Florida-Poly-IEEE-Computer-Society/Escape-Room/KiCad/Module 1/Module 1.kicad_pcb

## KiCad design Wiring/Multiplex Madness.kicad_sch

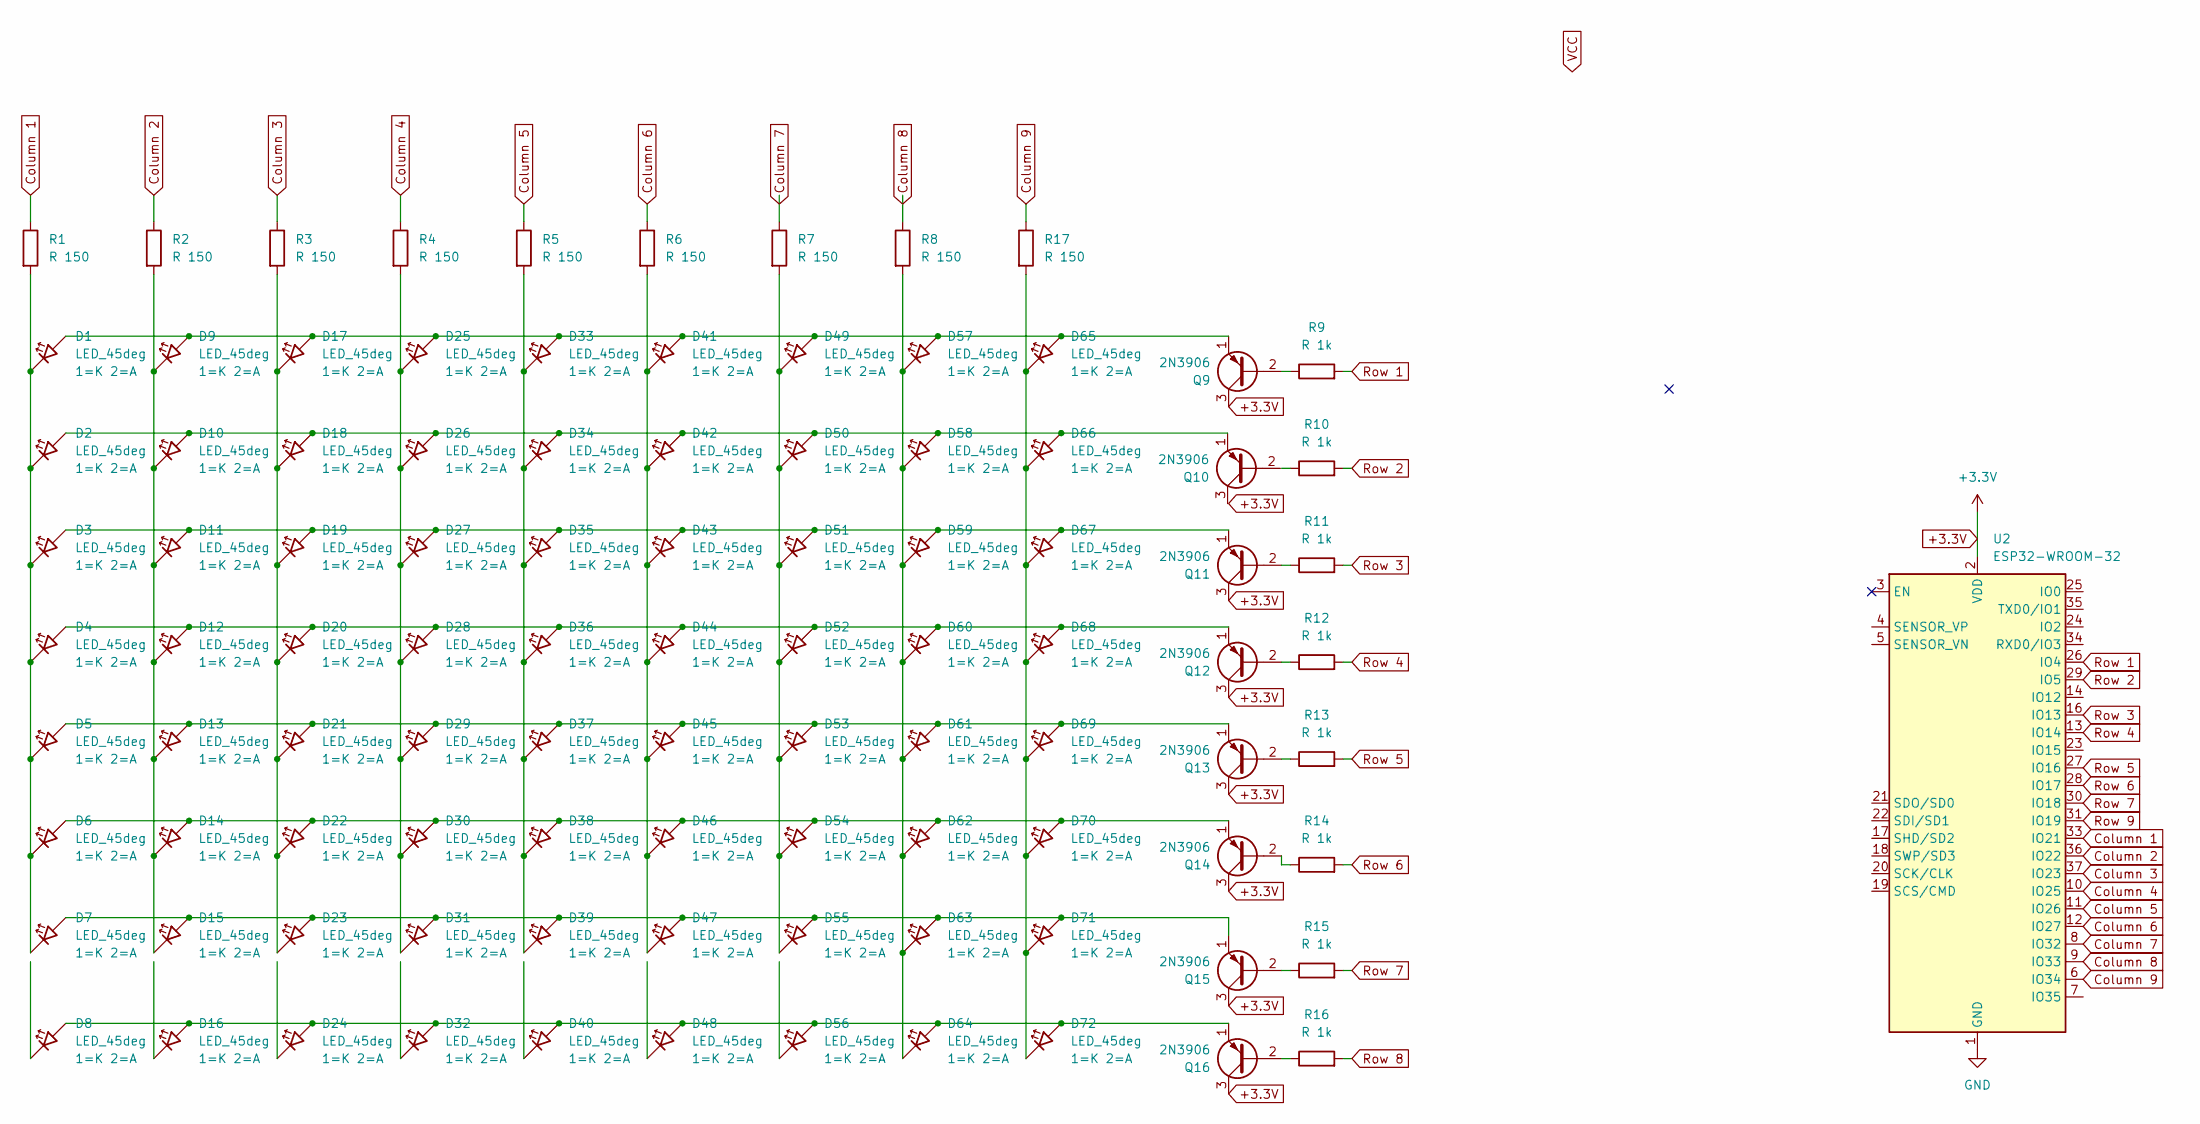
[picture p26: schematic Multiplex Madness.kicad_sch]

Parts:
D1, D2, D3, D4, D5, D6, D7, D8, D9, D10, D11, D12, D13, D14, D15, D16, D17, D18, D19, D20, D21, D22, D23, D24, D25, D26, D27, D28, D29, D30, D31, D32, D33, D34, D35, D36, D37, D38, D39, D40, D41, D42, D43, D44, D45, D46, D47, D48, D49, D50, D51, D52, D53, D54, D55, D56, D57, D58, D59, D60, D61, D62, D63, D64, D65, D66, D67, D68, D69, D70, D71, D72: LED_45deg
Q9, Q10, Q11, Q12, Q13, Q14, Q15, Q16: 2N3906; TO-92_Inline
R1, R2, R3, R4, R5, R6, R7, R8, R17: R 150
R9, R10, R11, R12, R13, R14, R15, R16: R 1k
U2: ESP32-WROOM-32

Connections:
+3.3V: Q9.3 (C), Q11.3 (C), Q12.3 (C), Q13.3 (C), Q14.3 (C), Q15.3 (C), Q16.3 (C), U2.2 (VDD)
Column 1: R1.1, U2.33 (IO21)
Column 2: R2.1, U2.36 (IO22)
Column 3: R3.1, U2.37 (IO23)
Column 4: R4.1, U2.10 (IO25)
Column 5: R5.1, U2.11 (IO26)
Column 6: R6.1, U2.12 (IO27)
Column 7: R7.1, U2.8 (IO32)
Column 8: R8.1, U2.9 (IO33)
Column 9: R17.1, U2.6 (IO34)
GND: U2.1 (GND), U2.15 (GND), U2.38 (GND), U2.39 (GND)
unnamed: D1.1 (K), D2.1 (K), D3.1 (K), D4.1 (K), D5.1 (K), D6.1 (K), D7.1 (K), R1.2
unnamed: D1.2 (A), D9.2 (A), D17.2 (A), D25.2 (A), D33.2 (A), D41.2 (A), D49.2 (A), D57.2 (A), D65.2 (A), Q9.1 (E)
unnamed: D9.1 (K), D10.1 (K), D11.1 (K), D12.1 (K), D13.1 (K), D14.1 (K), D15.1 (K), R2.2
unnamed: D2.2 (A), D10.2 (A), D18.2 (A), D26.2 (A), D34.2 (A), D42.2 (A), D50.2 (A), D58.2 (A), D66.2 (A), Q10.1 (E)
unnamed: D3.2 (A), D11.2 (A), D19.2 (A), D27.2 (A), D35.2 (A), D43.2 (A), D51.2 (A), D59.2 (A), D67.2 (A), Q11.1 (E)
unnamed: D4.2 (A), D12.2 (A), D20.2 (A), D28.2 (A), D36.2 (A), D44.2 (A), D52.2 (A), D60.2 (A), D68.2 (A), Q12.1 (E)
unnamed: D5.2 (A), D13.2 (A), D21.2 (A), D29.2 (A), D37.2 (A), D45.2 (A), D53.2 (A), D61.2 (A), D69.2 (A), Q13.1 (E)
unnamed: D6.2 (A), D14.2 (A), D22.2 (A), D30.2 (A), D38.2 (A), D46.2 (A), D54.2 (A), D62.2 (A), D70.2 (A), Q14.1 (E)
unnamed: D7.2 (A), D15.2 (A), D23.2 (A), D31.2 (A), D39.2 (A), D47.2 (A), D55.2 (A), D63.2 (A), D71.2 (A), Q15.1 (E)
unnamed: D8.2 (A), D16.2 (A), D24.2 (A), D32.2 (A), D40.2 (A), D48.2 (A), D56.2 (A), D64.2 (A), D72.2 (A), Q16.1 (E)
unnamed: D17.1 (K), D18.1 (K), D19.1 (K), D20.1 (K), D21.1 (K), D22.1 (K), D23.1 (K), R3.2
unnamed: D25.1 (K), D26.1 (K), D27.1 (K), D28.1 (K), D29.1 (K), D30.1 (K), D31.1 (K), R4.2
unnamed: D33.1 (K), D34.1 (K), D35.1 (K), D36.1 (K), D37.1 (K), D38.1 (K), D39.1 (K), R5.2
unnamed: D41.1 (K), D42.1 (K), D43.1 (K), D44.1 (K), D45.1 (K), D46.1 (K), D47.1 (K), R6.2
unnamed: D49.1 (K), D50.1 (K), D51.1 (K), D52.1 (K), D53.1 (K), D54.1 (K), D55.1 (K), R7.2
unnamed: D57.1 (K), D58.1 (K), D59.1 (K), D60.1 (K), D61.1 (K), D62.1 (K), D63.1 (K), D64.1 (K), R8.2
unnamed: D65.1 (K), D66.1 (K), D67.1 (K), D68.1 (K), D69.1 (K), D70.1 (K), D71.1 (K), D72.1 (K), R17.2
unnamed: Q9.2 (B), R9.1
unnamed: Q11.2 (B), R11.1
unnamed: Q12.2 (B), R12.1
unnamed: Q13.2 (B), R13.1
unnamed: Q14.2 (B), R14.1
unnamed: Q15.2 (B), R15.1
unnamed: Q16.2 (B), R16.1
Row 1: R9.2, U2.26 (IO4)
Row 2: R10.2, U2.29 (IO5)
Row 3: R11.2, U2.16 (IO13)
Row 4: R12.2, U2.13 (IO14)
Row 5: R13.2, U2.27 (IO16)
Row 6: R14.2, U2.28 (IO17)
Row 7: R15.2, U2.30 (IO18)
Row 8: R16.2
Row 9: U2.31 (IO19)
